MrRooby/dafi-crystal-led/board/dafi-crystal-led-rev-eng/dafi-crystal-led-rev-eng.kicad_pcb

## KiCad design controller_board/layout/board/board.kicad_sch

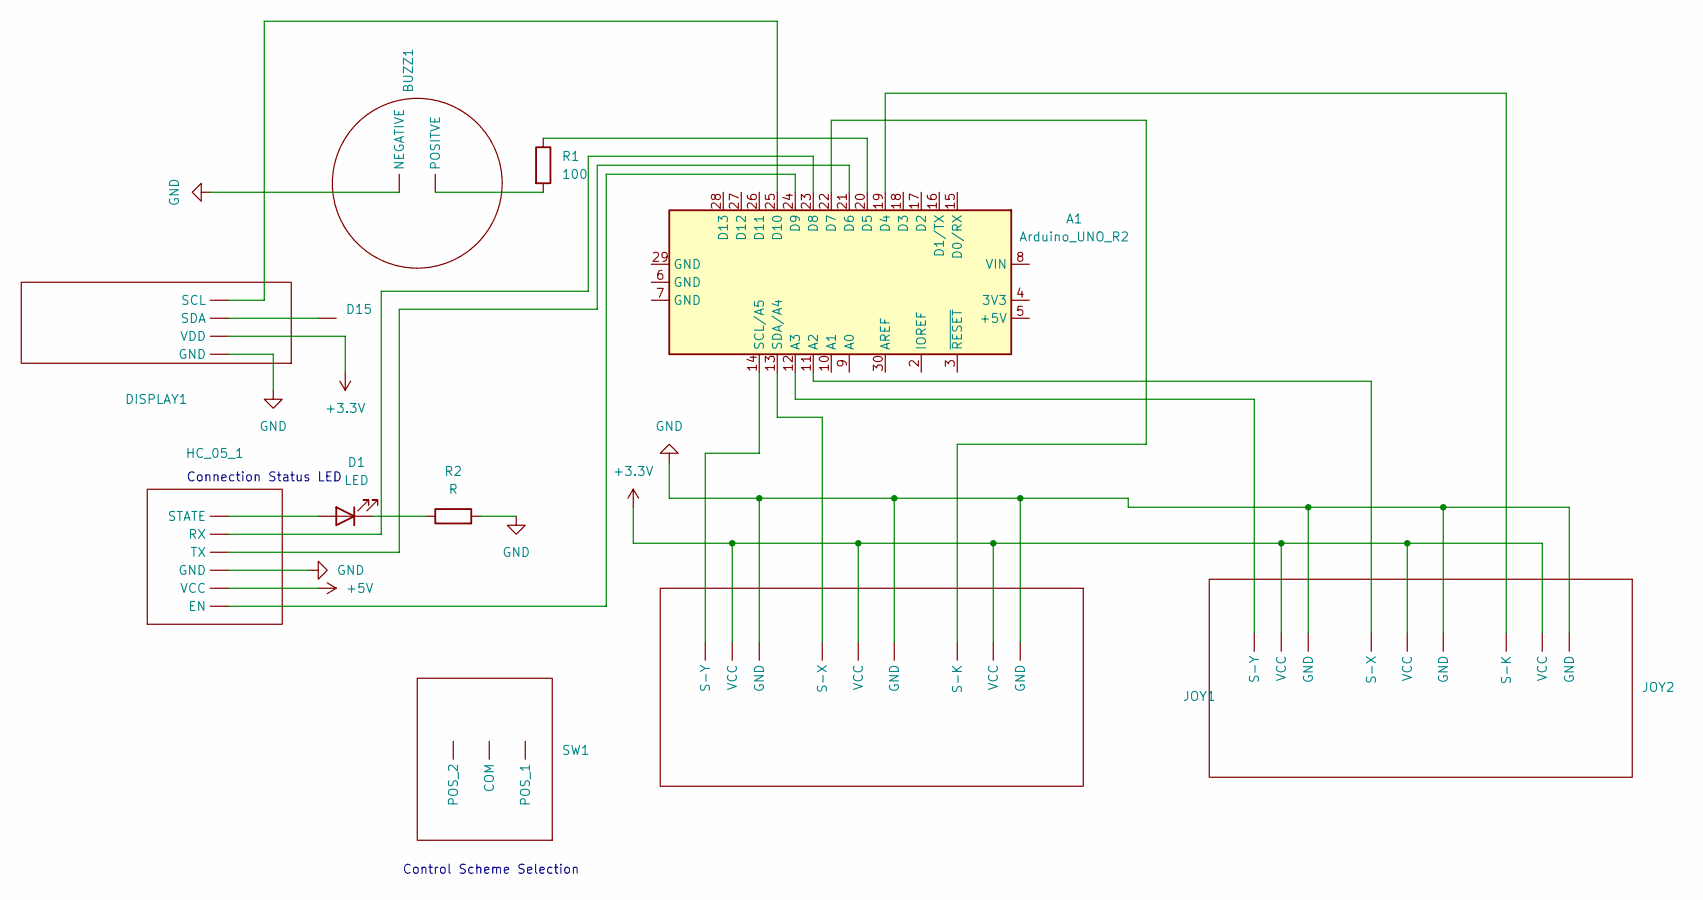
[picture p5: schematic board.kicad_sch]

Parts:
A1: Arduino_UNO_R2
BUZZ1: (no value)
D1: LED
D15: (no value)
DISPLAY1: (no value)
HC_05_1: (no value)
JOY1, JOY2: (no value)
R1: 100
R2: R
SW1: (no value)

Connections:
+3.3V: DISPLAY1., JOY1., JOY2.
+5V: HC_05_1.
GND: BUZZ1., DISPLAY1., HC_05_1., JOY1., JOY2., R2.2
unnamed: A1.11 (A2), JOY2.
unnamed: A1.12 (A3), JOY2.
unnamed: A1.13 (SDA/A4), JOY1.
unnamed: A1.14 (SCL/A5), JOY1.
unnamed: A1.19 (D4), JOY2.
unnamed: A1.20 (D5), R1.1
unnamed: A1.21 (D6), HC_05_1.
unnamed: A1.22 (D7), JOY1.
unnamed: A1.23 (D8), HC_05_1.
unnamed: A1.24 (D9), HC_05_1.
unnamed: A1.25 (D10), DISPLAY1.
unnamed: BUZZ1., R1.2
unnamed: D1.1 (K), R2.1
unnamed: D1.2 (A), HC_05_1.
unnamed: D15., DISPLAY1.

Notes on the sheet:
Connection Status LED
Control Scheme Selection
